SpiLiam/GBC-CR2025-FlexHolder/supports de pile cr2025 GBC.kicad_sch

## KiCad design supports de pile cr2025 GBC.kicad_sch (2026-05-12)

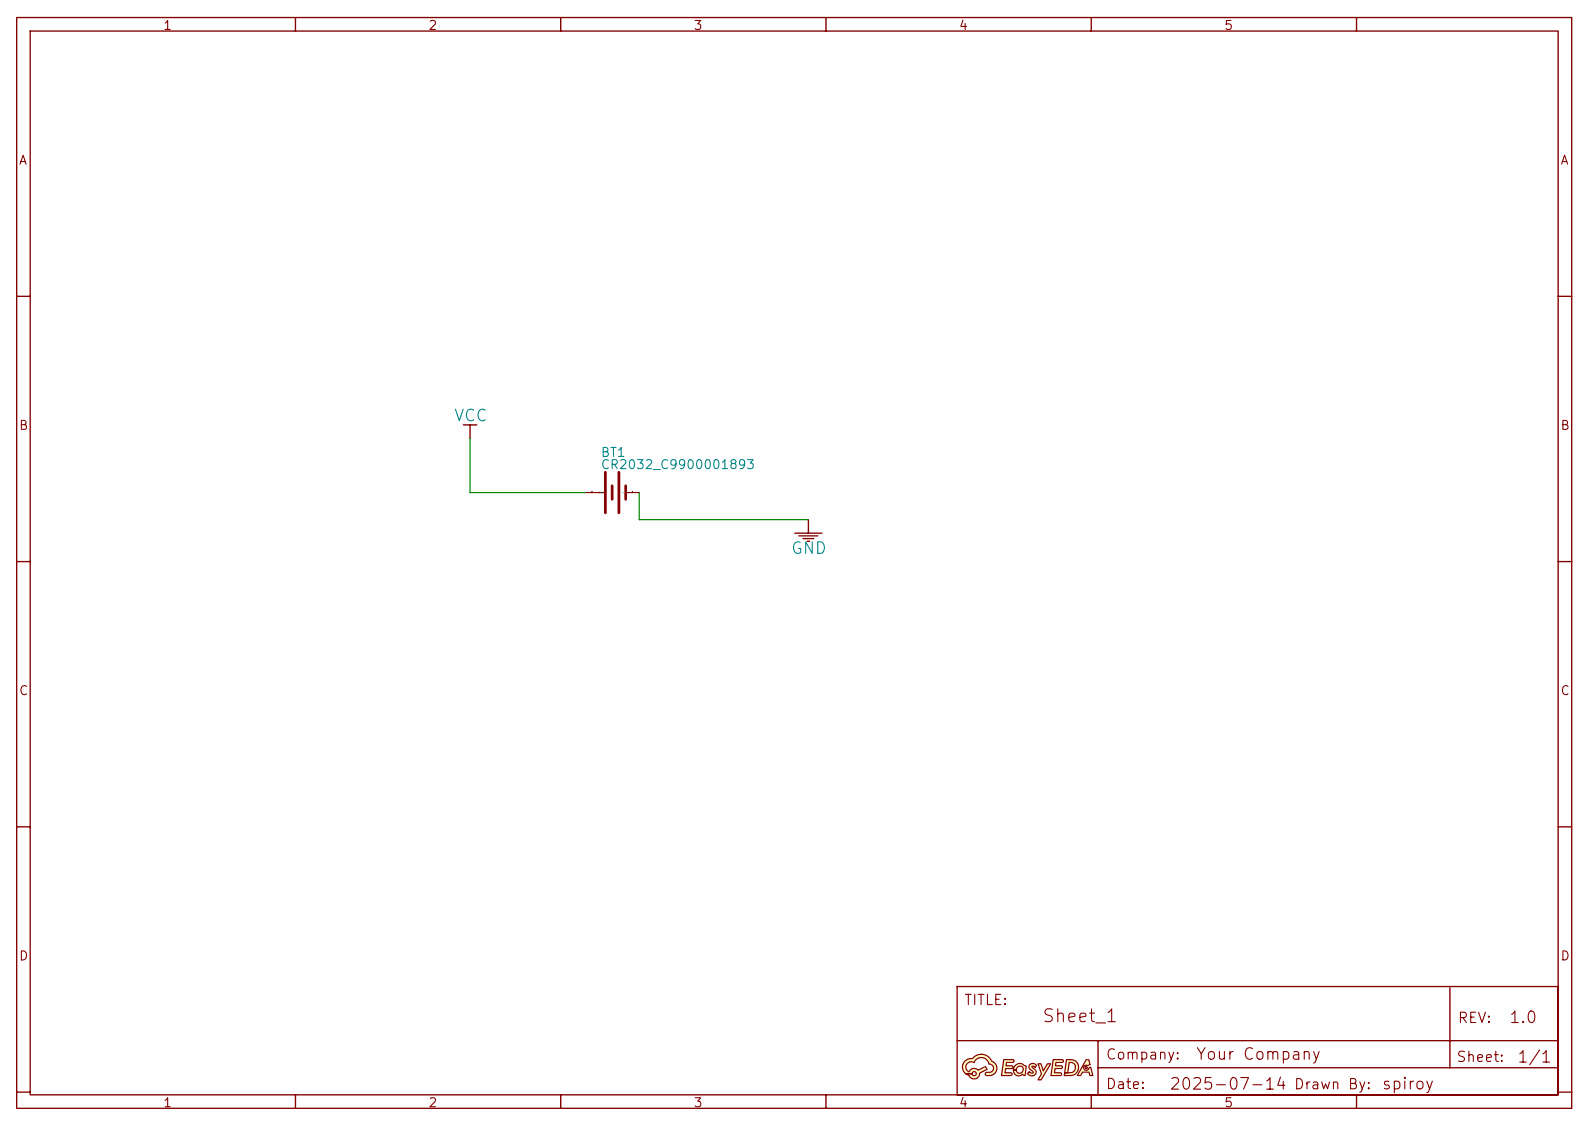
[picture p16: schematic supports de pile cr2025 GBC.kicad_sch]

Parts:
A: A; Manufacturer Part ?
BT1: CR2032_C9900001893; Manufacturer Part CR2032
